JoseitoOliveira/Samart-Button/Imagens/IMG_20190511_115959.jpg

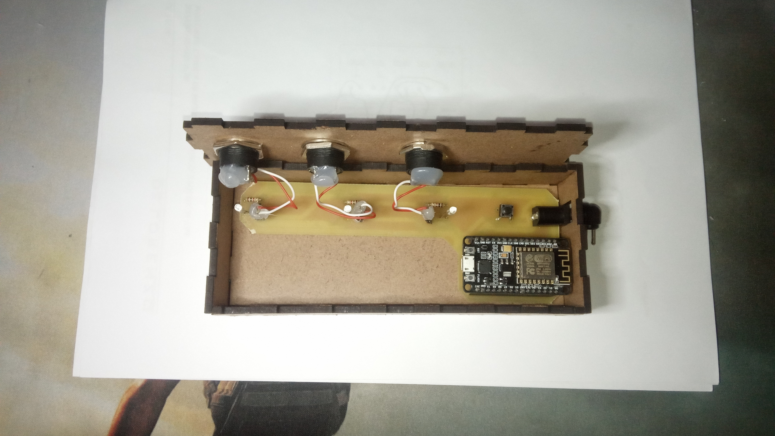
Imagens/IMG_20190511_115959.jpg
