JoseitoOliveira/Samart-Button/Imagens/IMG_20190511_120140.jpg

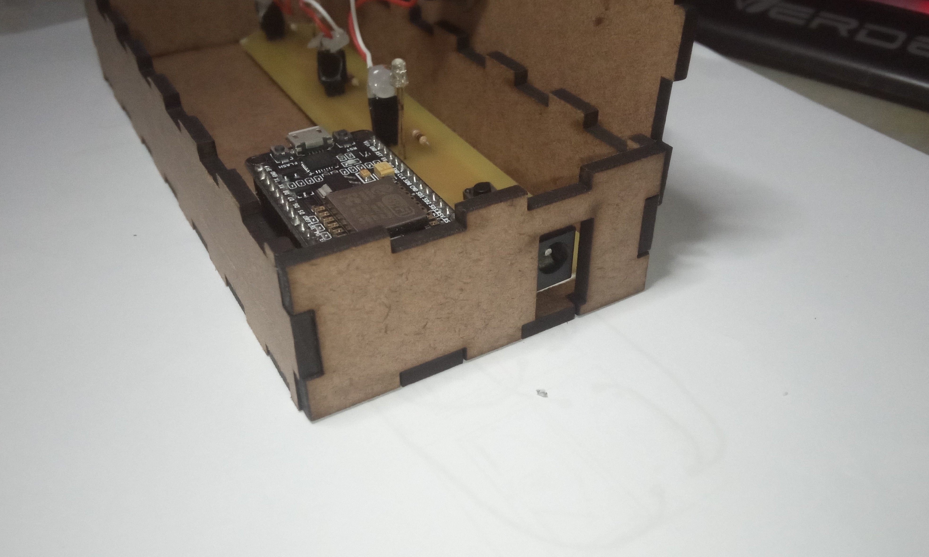
Imagens/IMG_20190511_120140.jpg
